be1ieve/esp32cam-tinycamera/pcb/PCB.png

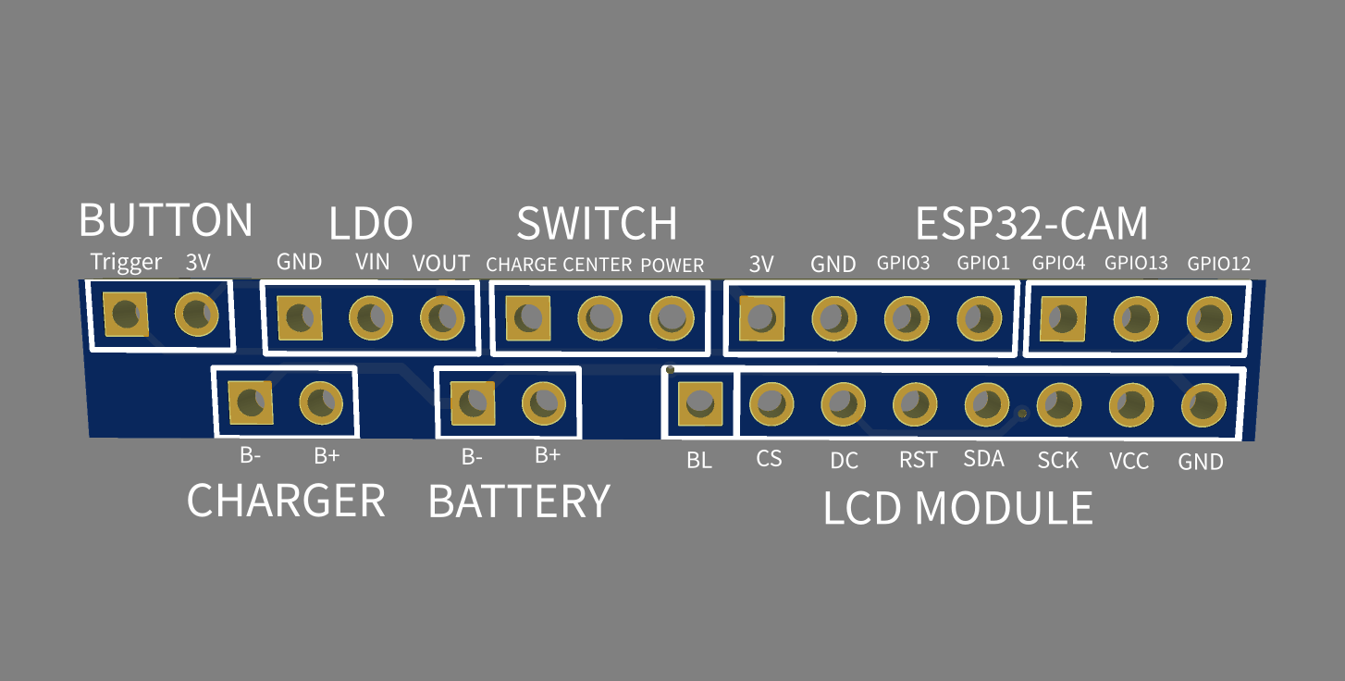
pcb/PCB.png
