be1ieve/esp32cam-tinycamera/pic/horizontal/backview2.jpg

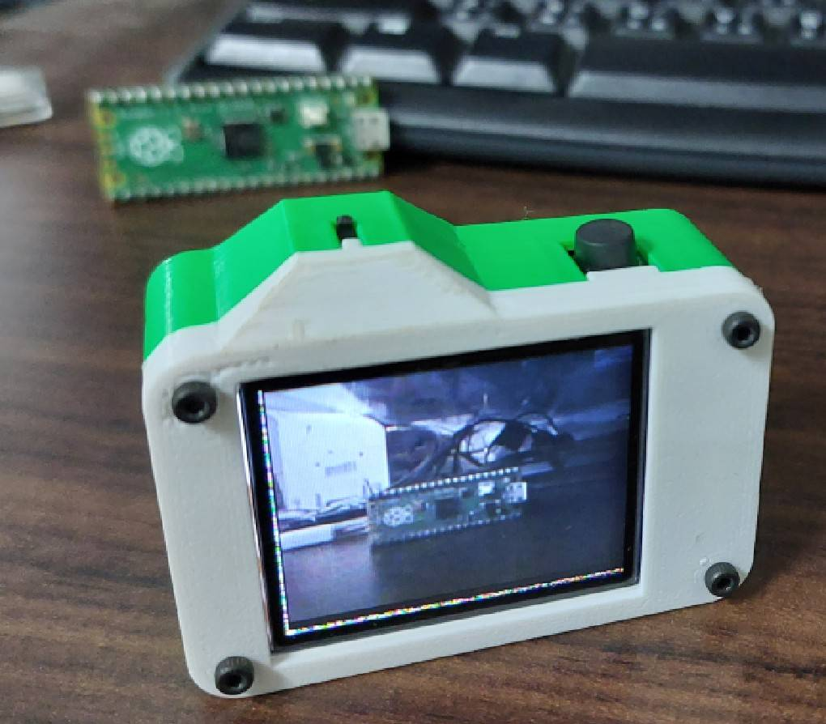
pic/horizontal/backview2.jpg
