be1ieve/esp32cam-tinycamera/pic/horizontal/frontview2.jpg

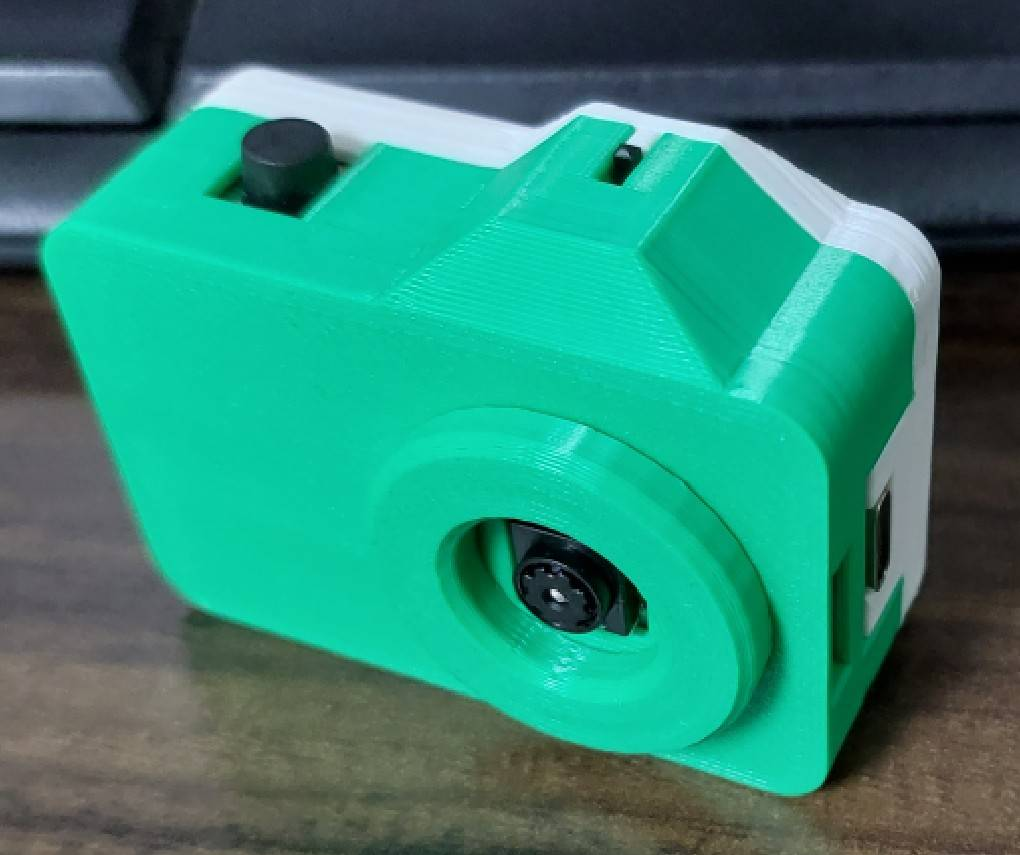
pic/horizontal/frontview2.jpg
