be1ieve/esp32cam-tinycamera/pic/horizontal/pcbassambly.jpg

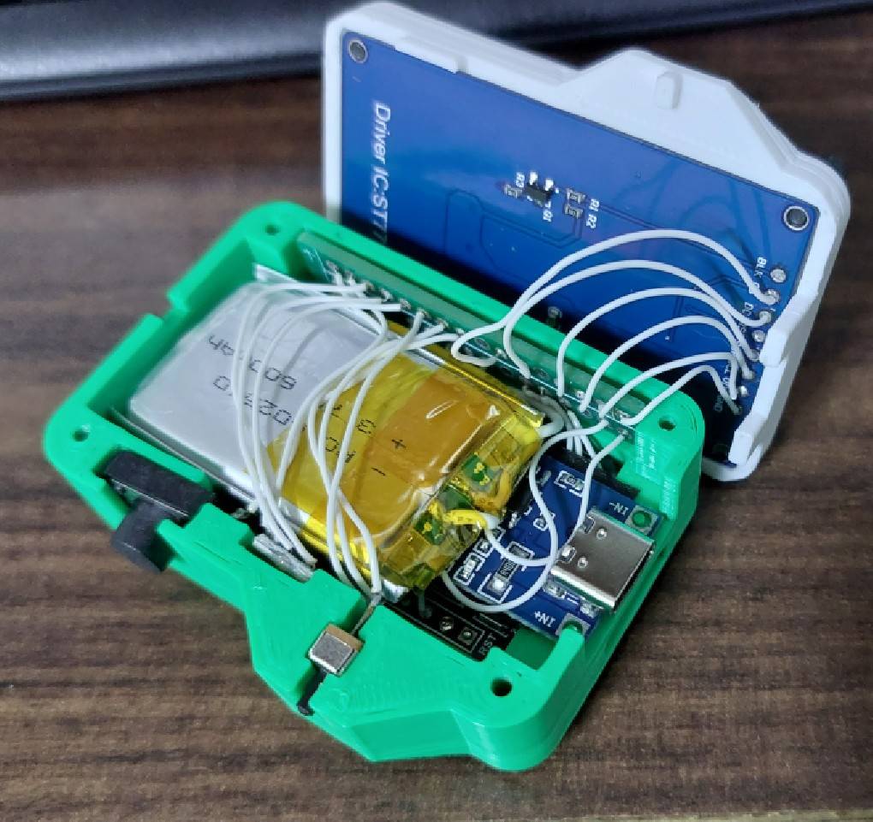
pic/horizontal/pcbassambly.jpg
