be1ieve/esp32cam-tinycamera/pic/mapping.png

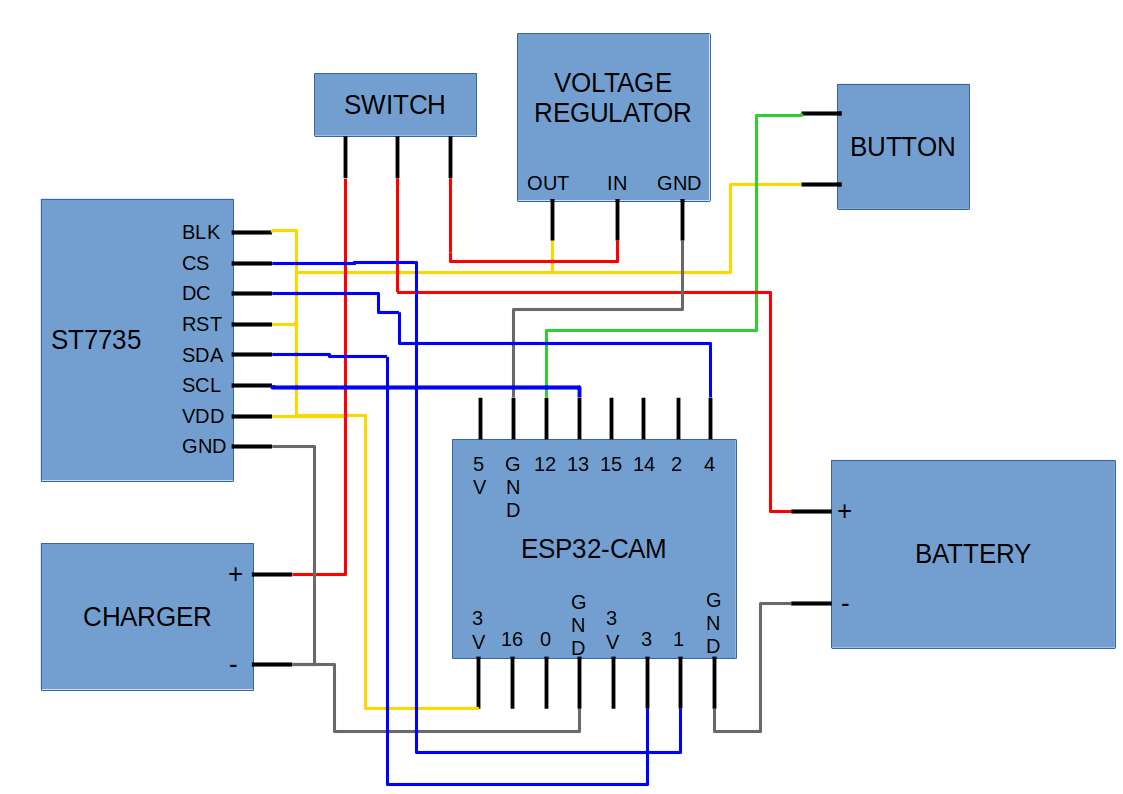
pic/mapping.png
