be1ieve/esp32cam-tinycamera/pic/products.jpg

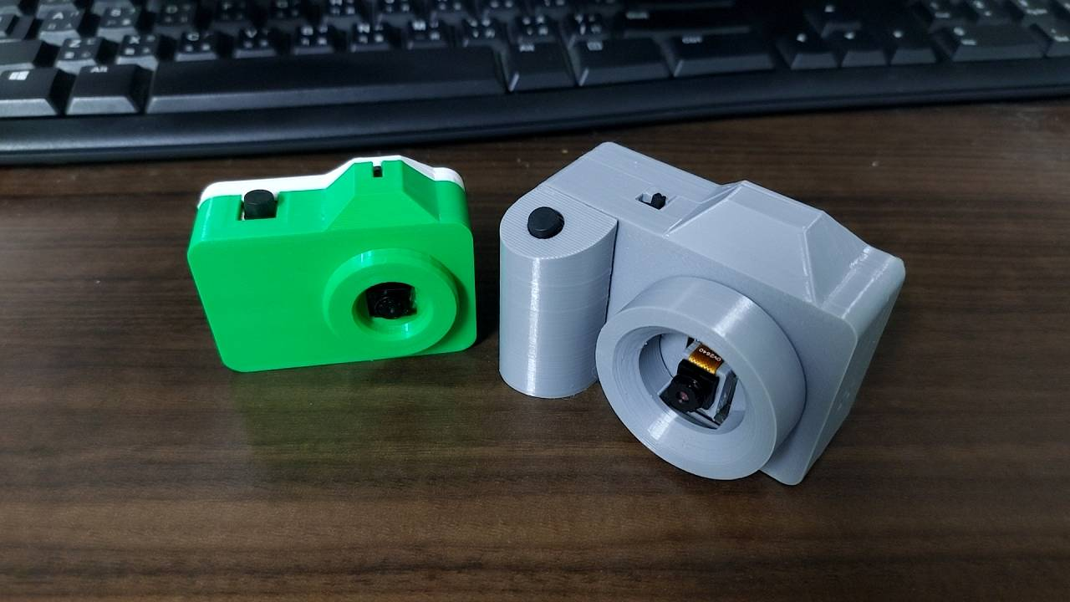
pic/products.jpg
