be1ieve/esp32cam-tinycamera/pic/vertical/3d-back.png

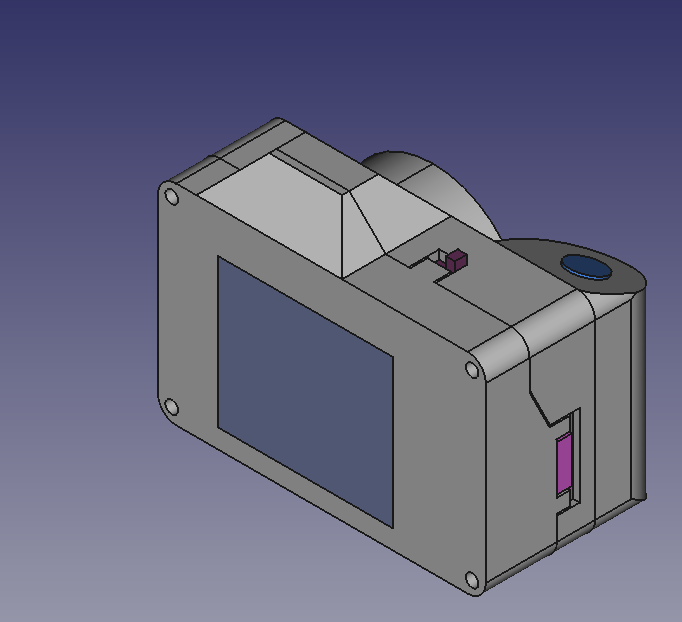
pic/vertical/3d-back.png
