be1ieve/esp32cam-tinycamera/pic/vertical/3d-front.png

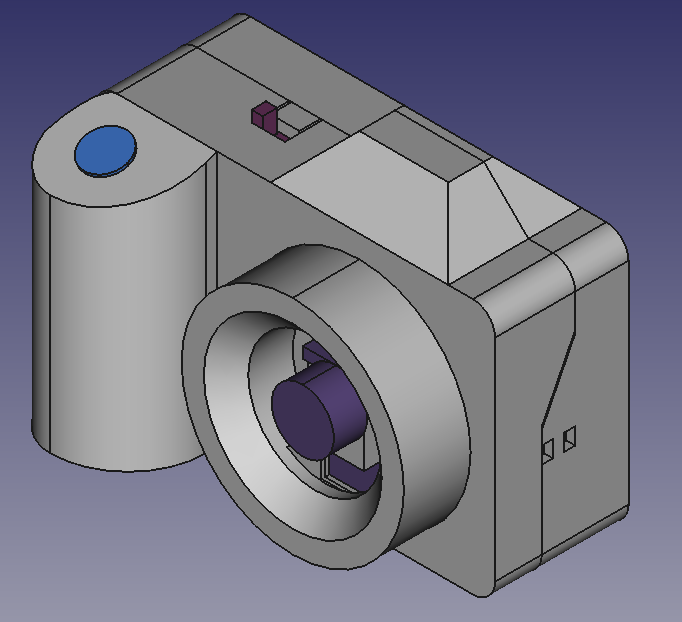
pic/vertical/3d-front.png
