be1ieve/esp32cam-tinycamera/pic/vertical/allignment.png

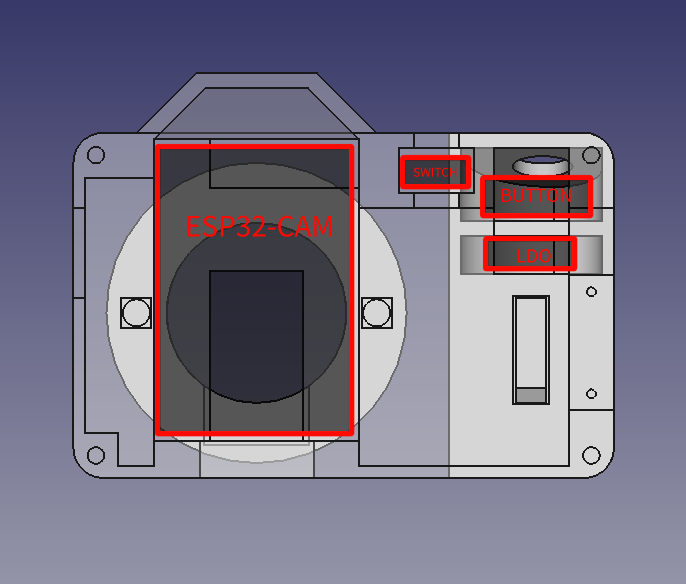
pic/vertical/allignment.png
