be1ieve/esp32cam-tinycamera/pic/vertical/explode.png

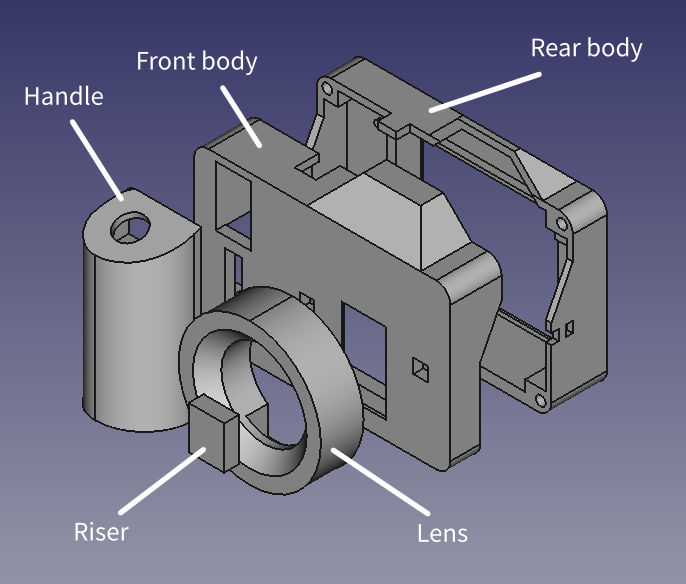
pic/vertical/explode.png
