be1ieve/esp32cam-tinycamera/pic/vertical/inside.jpg

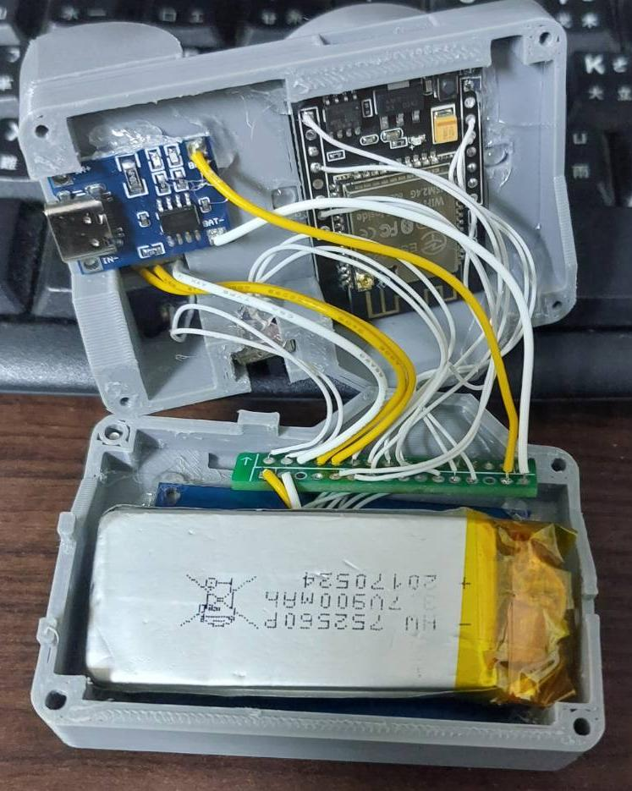
pic/vertical/inside.jpg
