be1ieve/esp32cam-tinycamera/pic/vertical/placing.png

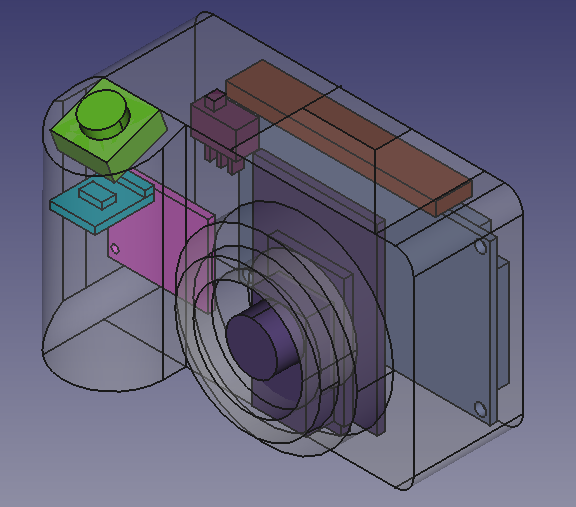
pic/vertical/placing.png
