be1ieve/esp32cam-tinycamera/pic/vertical/printing.png

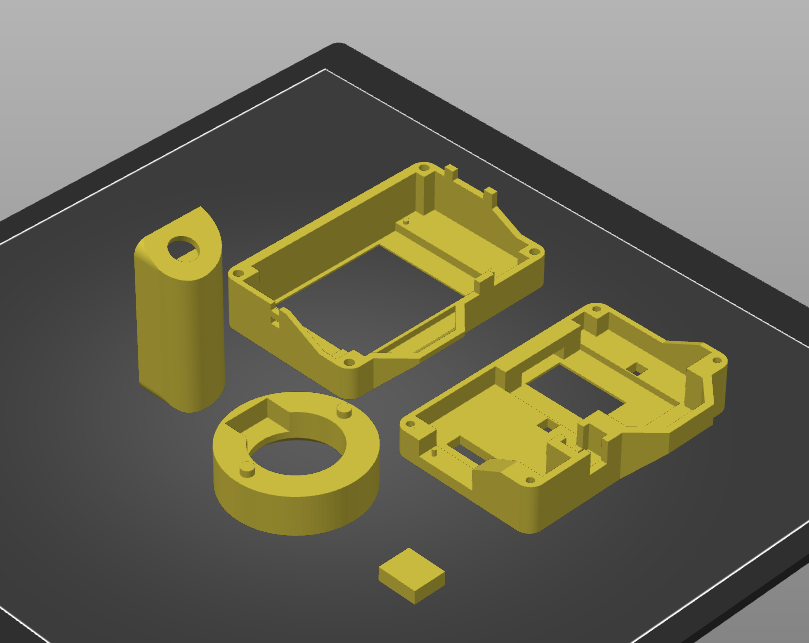
pic/vertical/printing.png
